nikor30/rs232_mobile/firmware/src/sdcard.cpp

#include "sdcard.h"

#include <FS.h>
#include <SD.h>
#include <SPI.h>
#include <Preferences.h>
#include "display.h"

namespace Sd {

static const uint32_t FLUSH_MS = 2000;     // SD writes are slow: collect, then flush
static const size_t   BUF_SIZE = 1024;

static bool ok = false;
static SPIClass &spi = SPI;                // LovyanGFX has opened this bus for the LCD

// The bus is shared with the LCD: the display task and the card must take turns.
struct BusGuard {
  BusGuard() { Display::busLock(); }
  ~BusGuard() { Display::busUnlock(); }
};

// Diagnostic trail, kept in flash so it survives the resets it is about: how
// each start went ("K" after power-on, "R" after a reset, "+" mounted, "-xx" not
// mounted with the card's answer) and "!<s>" when a mounted card stopped
// answering after that many seconds.
static String hist;
static bool histLoaded = false;
static void note(const String &event) {
  Preferences p;
  p.begin("sddiag", false);
  if (!histLoaded) { hist = p.getString("hist", ""); histLoaded = true; }
  hist += (hist.length() ? " " : "") + event;
  while (hist.length() > 160) {
    int sp = hist.indexOf(' ');
    hist = sp < 0 ? String() : hist.substring(sp + 1);
  }
  p.putString("hist", hist);
  p.end();
}
String history() {
  if (!histLoaded) {
    Preferences p;
    p.begin("sddiag", true);
    hist = p.getString("hist", "");
    p.end();
    histLoaded = true;
  }
  return "Verlauf: " + hist;
}

struct Log {
  File f;
  String name;
  uint32_t bytes = 0;
  uint8_t buf[BUF_SIZE];
  size_t len = 0;
  uint32_t lastFlush = 0;
};
static Log logs[MAX_PORTS];

// usedBytes() walks the whole allocation table - seconds on a large card. The
// front ends ask on every redraw, so the figures are taken once and refreshed
// when a recording ends.
static uint64_t cachedTotalMb = 0, cachedUsedMb = 0;
static void refreshSizes() {
  BusGuard guard;
  cachedTotalMb = SD.totalBytes() / (1024ULL * 1024ULL);
  cachedUsedMb = SD.usedBytes() / (1024ULL * 1024ULL);
}

bool mounted() { return ok; }
uint64_t totalMb() { return ok ? cachedTotalMb : 0; }
uint64_t usedMb() { return ok ? cachedUsedMb : 0; }

const char *typeName() {
  if (!ok) return "keine Karte";
  switch (SD.cardType()) {
    case CARD_MMC:  return "MMC";
    case CARD_SD:   return "SDSC";
    case CARD_SDHC: return "SDHC";
    default:        return "unbekannt";
  }
}

bool begin() {
  if (ok) return true;
  static uint32_t lastFailure = 0;       // setup() asks twice on boards that start the card early
  if (lastFailure && millis() - lastFailure < 5000) return false;
  BusGuard guard;
  static bool firstAttempt = true;
  const char *boot = esp_reset_reason() == ESP_RST_POWERON ? "K" : "R";
  // Called before the LCD is started (see lcd_ui.cpp): a card fresh from power-up
  // still listens in SD mode, where it ignores chip select and would take the
  // display traffic for commands. It has to be switched to SPI mode first.
  spi.begin(PIN_SD_SCLK, PIN_SD_MISO, PIN_SD_MOSI, -1);
  // 20 MHz is conservative.
  // A card that kept its power through a reset sometimes misses the first
  // attempt, so try again, slower.
  for (uint32_t hz : {20000000u, 10000000u, 4000000u}) {
    ok = SD.begin(PIN_SD_CS, spi, hz);
    if (ok) break;
    SD.end();
    delay(100);
  }
  if (!ok) {
    // Say what the slot answers to a bare CMD0, so "no card" can be told from
    // "card does not start": 01 = card present and idle, FF = nothing answers.
    pinMode(PIN_SD_MISO, INPUT_PULLUP);
    spi.beginTransaction(SPISettings(400000, MSBFIRST, SPI_MODE0));
    digitalWrite(PIN_SD_CS, HIGH);
    for (int i = 0; i < 10; i++) spi.transfer(0xFF);
    digitalWrite(PIN_SD_CS, LOW);
    const uint8_t cmd0[] = {0x40, 0, 0, 0, 0, 0x95};
    for (uint8_t b : cmd0) spi.transfer(b);
    uint8_t r[8];
    for (uint8_t &b : r) b = spi.transfer(0xFF);
    digitalWrite(PIN_SD_CS, HIGH);
    spi.transfer(0xFF);
    spi.endTransaction();
    Serial.printf("[SD]   keine Karte gefunden (Antwort auf CMD0: %02X %02X %02X %02X %02X %02X %02X %02X)\n",
                  r[0], r[1], r[2], r[3], r[4], r[5], r[6], r[7]);
    if (firstAttempt) {
      char ev[8];
      snprintf(ev, sizeof(ev), "%s-%02X", boot, r[0]);
      note(ev);
    }
    firstAttempt = false;
    lastFailure = millis() | 1;
    return false;
  }
  if (firstAttempt) note(String(boot) + "+");
  firstAttempt = false;
  if (!SD.exists("/logs")) SD.mkdir("/logs");
  if (!SD.exists("/configs")) SD.mkdir("/configs");
  if (!SD.exists("/xfer")) SD.mkdir("/xfer");
  refreshSizes();
  Serial.printf("[SD]   %s, %llu von %llu MB belegt\n", typeName(), usedMb(), totalMb());
  return true;
}

// There is no clock in this device, so files are numbered instead of dated.
static String nextName(uint8_t port) {
  for (uint16_t i = 1; i < 1000; i++) {
    char p[32];
    snprintf(p, sizeof(p), "/logs/port%u-%03u.log", (unsigned)(port + 1), (unsigned)i);
    if (!SD.exists(p)) return String(p);
  }
  return String();
}

bool logStart(uint8_t port) {
  if (!ok || port >= MAX_PORTS || logs[port].f) return false;
  BusGuard guard;
  String n = nextName(port);
  if (!n.length()) return false;
  logs[port].f = SD.open(n, FILE_WRITE);
  if (!logs[port].f) return false;
  logs[port].name = n;
  logs[port].bytes = 0;
  logs[port].len = 0;
  logs[port].lastFlush = millis();
  Serial.printf("[SD]   Mitschnitt Port %u -> %s\n", port + 1, n.c_str());
  return true;
}

static void flush(uint8_t port) {
  Log &l = logs[port];
  if (!l.f || !l.len) return;
  BusGuard guard;
  l.f.write(l.buf, l.len);
  l.f.flush();
  l.len = 0;
  l.lastFlush = millis();
}

void logStop(uint8_t port) {
  if (port >= MAX_PORTS || !logs[port].f) return;
  BusGuard guard;
  flush(port);
  logs[port].f.close();
  logs[port].name = "";
  refreshSizes();
}

bool logging(uint8_t port) { return port < MAX_PORTS && logs[port].f; }
String logName(uint8_t port) { return port < MAX_PORTS ? logs[port].name : String(); }
uint32_t logBytes(uint8_t port) { return port < MAX_PORTS ? logs[port].bytes : 0; }

void write(uint8_t port, const uint8_t *data, size_t len) {
  if (port >= MAX_PORTS || !logs[port].f) return;
  Log &l = logs[port];
  for (size_t i = 0; i < len; i++) {
    l.buf[l.len++] = data[i];
    if (l.len == BUF_SIZE) flush(port);
  }
  l.bytes += len;
}

void end() {
  if (!ok) return;
  for (uint8_t p = 0; p < MAX_PORTS; p++) logStop(p);
  BusGuard guard;
  SD.end();
  ok = false;
}

void loop() {
  if (!ok) return;
  uint32_t now = millis();
  // Is the card still there? Reads one raw sector every 20 s. On the shared bus
  // a card has been seen to stop answering; this pins down when.
  static uint32_t lastCheck = 0;
  static uint8_t sector[512];
  if (now - lastCheck > 20000) {
    lastCheck = now;
    BusGuard guard;
    if (!SD.readRAW(sector, 0)) {
      Serial.printf("[SD]   Karte antwortet nicht mehr (nach %lu s Betrieb)\n", (unsigned long)(now / 1000));
      note("!" + String(now / 1000) + "s");
      for (uint8_t p = 0; p < MAX_PORTS; p++)
        if (logs[p].f) { logs[p].f.close(); logs[p].name = ""; }
      SD.end();
      ok = false;
      return;
    }
  }
  for (uint8_t p = 0; p < MAX_PORTS; p++)
    if (logs[p].f && logs[p].len && now - logs[p].lastFlush > FLUSH_MS) flush(p);
}

}  // namespace Sd
