nikor30/rs232_mobile/firmware/src/sdcard.h

#pragma once
#include <Arduino.h>
#include "config.h"

// SD card (SPI). Everything here is a no-op when no
// card is present, so the console keeps working without one.
//
//   /logs/<port>-<nnn>.log   session recordings, one file per port and boot
//   /configs/*.txt           configurations that can be played back to a device
//   /xfer/*                  images for XMODEM/YMODEM transfers
namespace Sd {
  bool begin();                       // false = no card
  bool mounted();
  uint64_t totalMb();
  uint64_t usedMb();
  const char *typeName();
  String history();                   // diagnostic trail of mounts and failures (debug console)

  // ---- session log ----
  bool logStart(uint8_t port);        // opens the next free file for that port
  void logStop(uint8_t port);
  bool logging(uint8_t port);
  String logName(uint8_t port);       // "" when not logging
  uint32_t logBytes(uint8_t port);
  void write(uint8_t port, const uint8_t *data, size_t len);   // ignored unless logging
  void loop();                        // flushes at most every FLUSH_MS
  void end();                         // close the recordings and release the card (before power-off)
}
